NNNILabs/6.5-Digit-Multislope-ADC/PCB3/20210821_142343.jpg

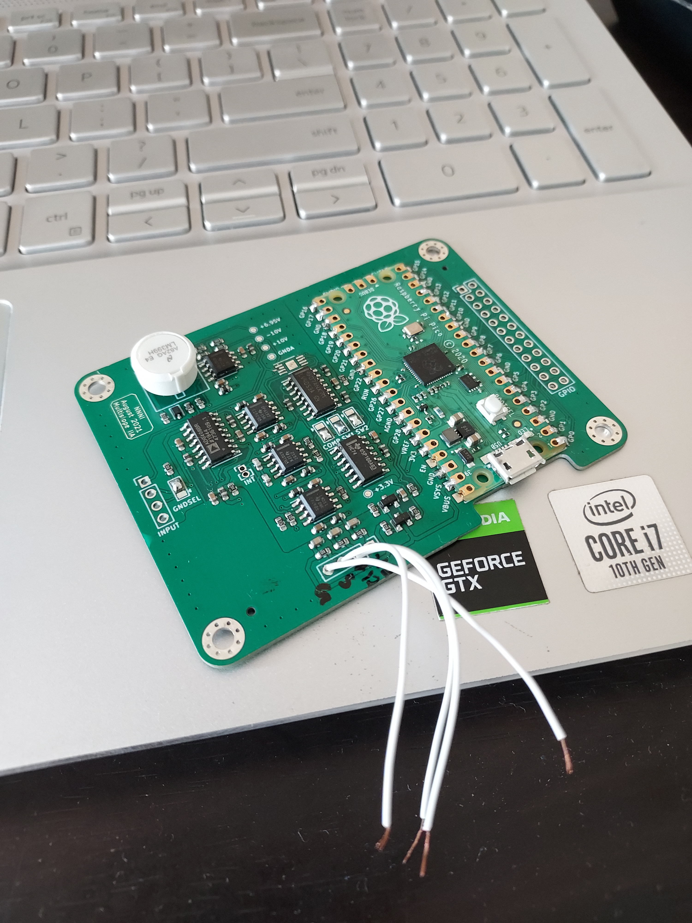
PCB3/20210821_142343.jpg
